bencan1a/chainsword/G6.stl

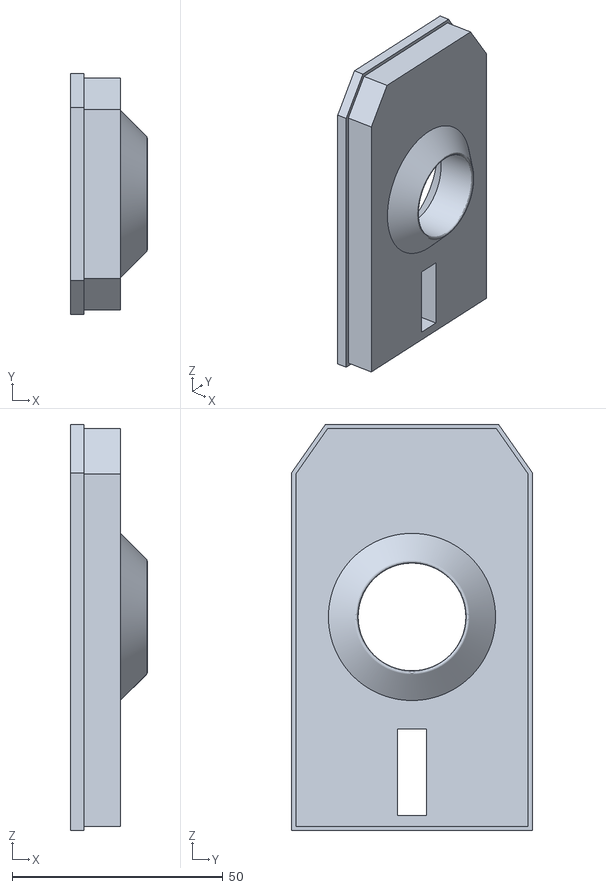
[picture p15: CAD file, 2025-01-07]
G6.stl
18.1 x 57.1 x 96.2
