bencan1a/chainsword/PowerSwitch Cover.stl

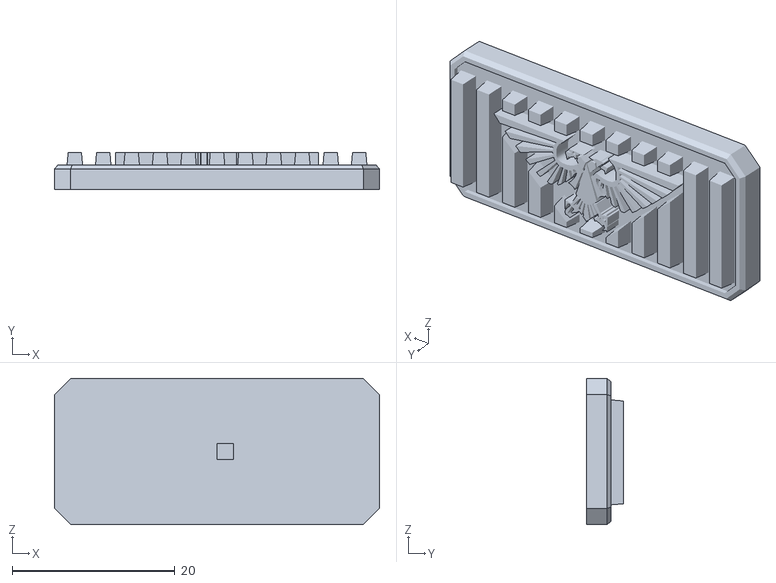
[picture p16: CAD file, 2025-01-07]
PowerSwitch Cover.stl
40.0 x 4.50 x 18.0
